promesoft/KicadFormantVCO/vco_ltspice_tests/test_schmitt.asc

C1: cap; 470p
D1: zener; 1N750
I1: current; {ITUNE}; load
Q3: npn; BC547C
R1: res; 50K
R2: res; 50K
R3: res; 200K
R4: res; 1000
R5: res; 200
R6: res; 1k
R7: res; 1000000
U1: OP492
U2: OP492
V1: voltage; 15
V2: voltage; 15
Named nets: 0
.tran 0 30m 0 startup
.param ITUNE=I
.step oct param ITUNE 0.1u 20u 1
